MOSH-Insa-Toulouse/5ISS-Bouzergan-Griebenow-Housni/LTSpice files/capteur.asc

B1: bi; I=V(cp,cn)*(10n+(v(gc,gn)*10n))
C1: cap; 200µ
R1: res; 1k
Named nets: gc, cp, cn, gp, gn
